vinmarshall/Radio-Shack-Music-Maker/images/pcb.bmp

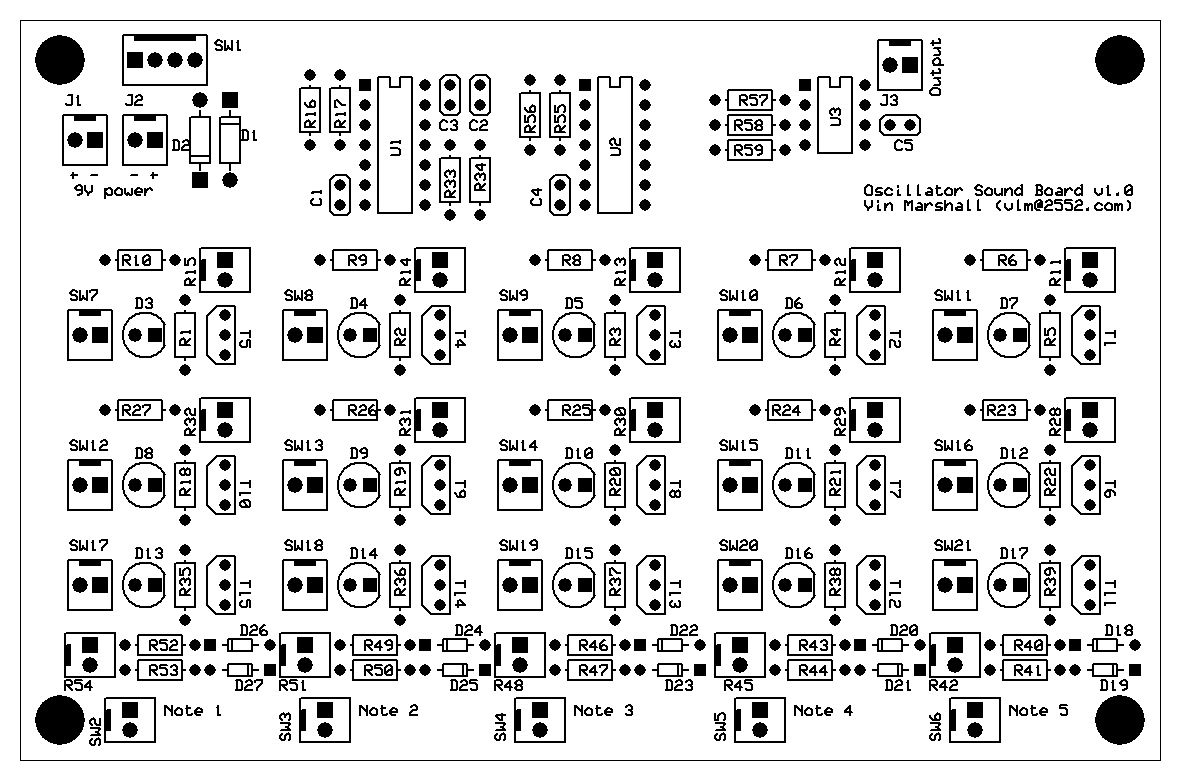
images/pcb.bmp
