vinmarshall/Radio-Shack-Music-Maker/images/prototype_002.jpg

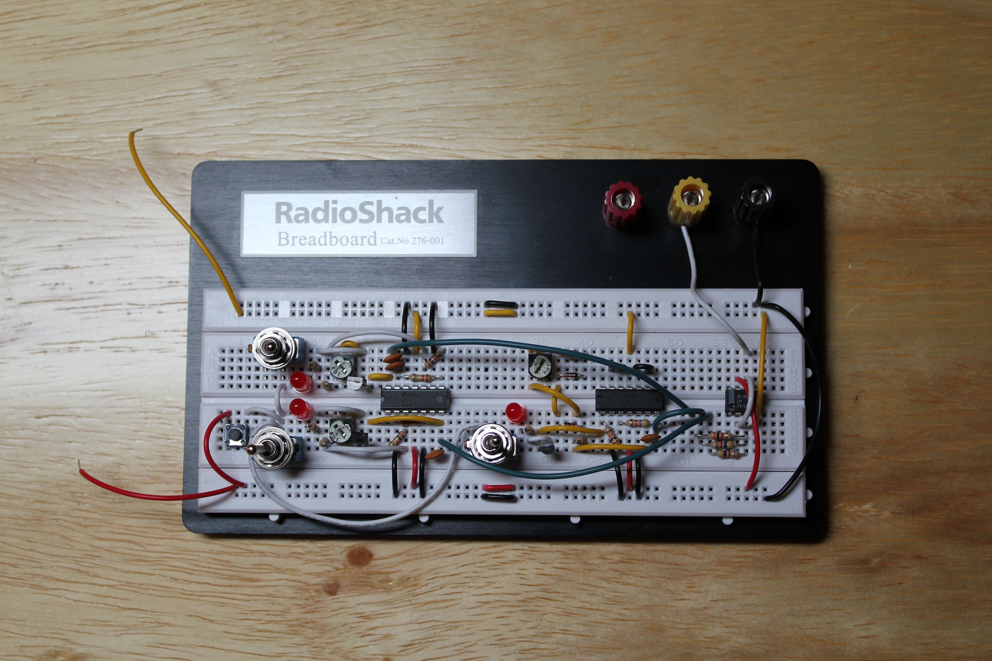
images/prototype_002.jpg
