vinmarshall/Radio-Shack-Music-Maker/schematic/5_oscillator_3.bmp

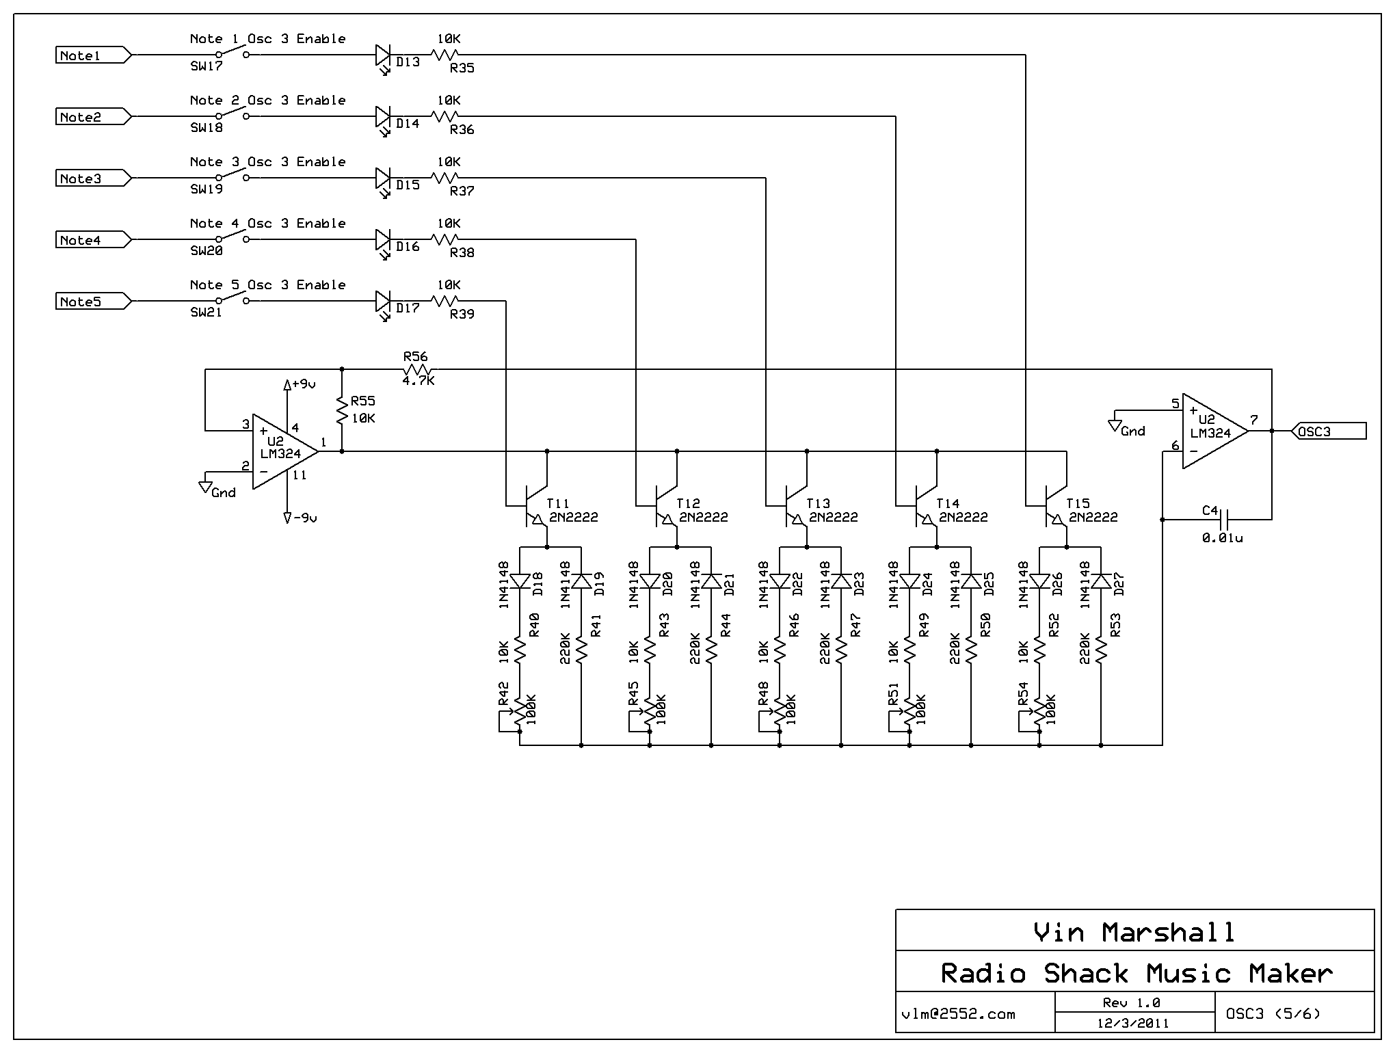
schematic/5_oscillator_3.bmp
