vinmarshall/Radio-Shack-Music-Maker/images/assembly.png

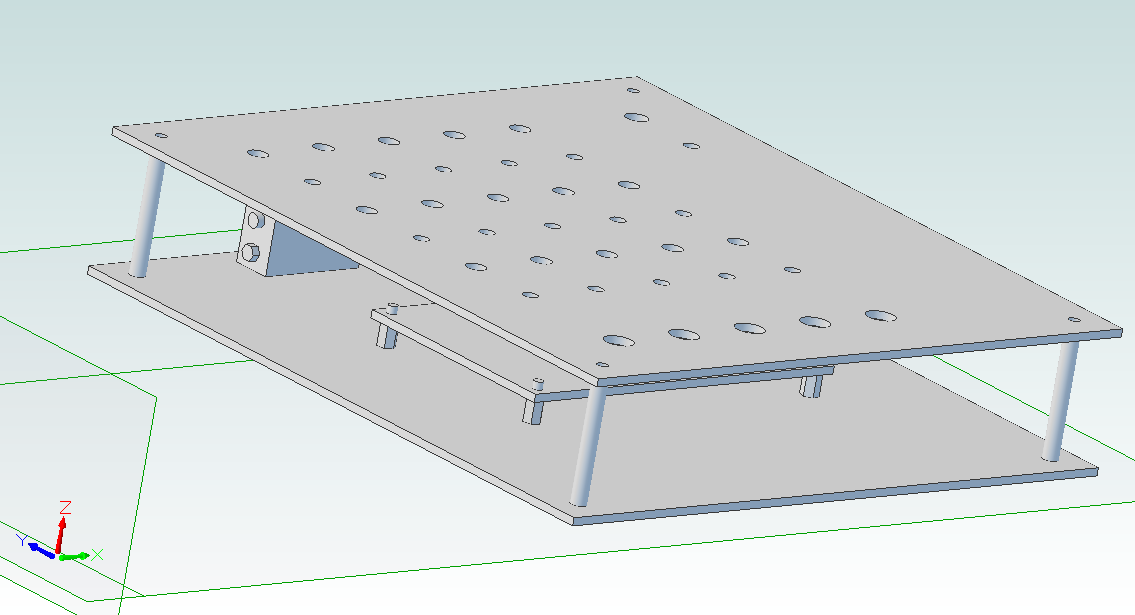
images/assembly.png
